dani007200964/Viking-Skull-Lamp/CAD/textures/galaxy_black_diffuse.png

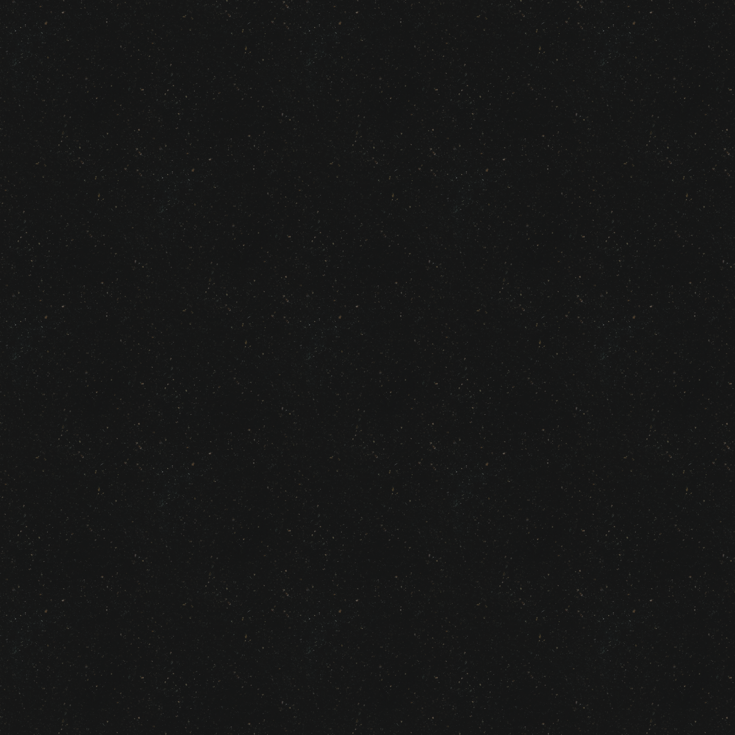
CAD/textures/galaxy_black_diffuse.png
