dani007200964/Viking-Skull-Lamp/CAD/textures/galaxy_black_specular.png

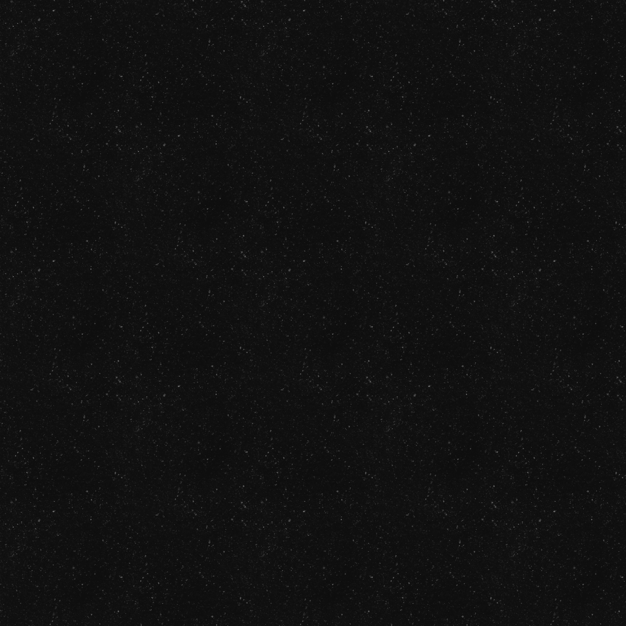
CAD/textures/galaxy_black_specular.png
