dani007200964/Viking-Skull-Lamp/docs/images/poster.png

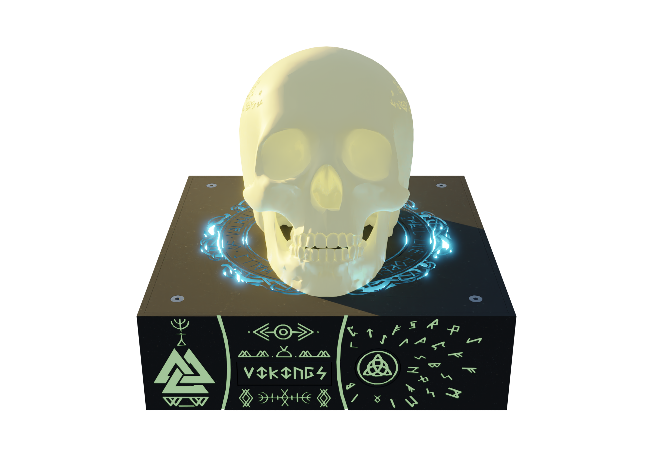
docs/html/poster.png
