dani007200964/Viking-Skull-Lamp/CAD/3mf/encoder_knob_with_art_1pcs.3mf

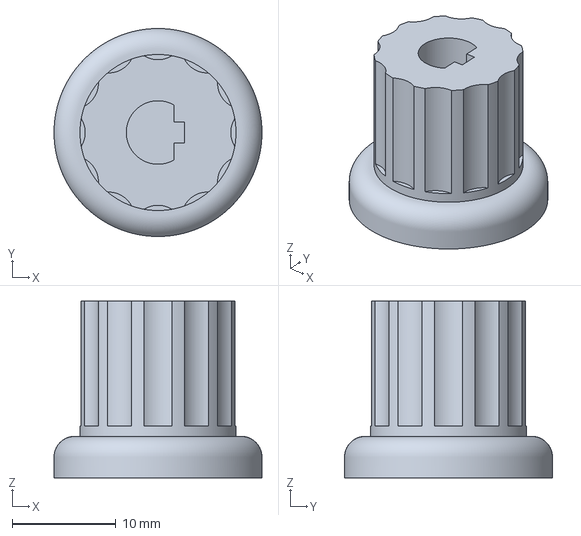
[picture p32: CAD file, 2022-09-24]
CAD/3mf/encoder_knob_with_art_1pcs.3mf
20.0 x 20.0 x 17.0 mm
