dani007200964/Viking-Skull-Lamp/CAD/3mf/led_ring_mount_1pcs.3mf

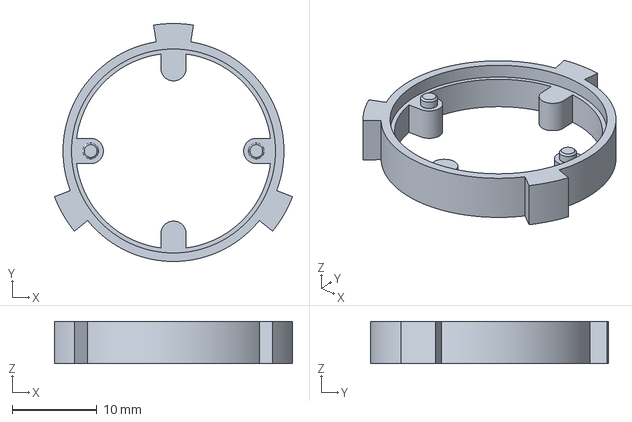
[picture p33: CAD file, 2022-09-24]
CAD/3mf/led_ring_mount_1pcs.3mf
28.0 x 28.0 x 5.00 mm
