dani007200964/Viking-Skull-Lamp/docs/html/box_front_with_art_1pcs.3mf

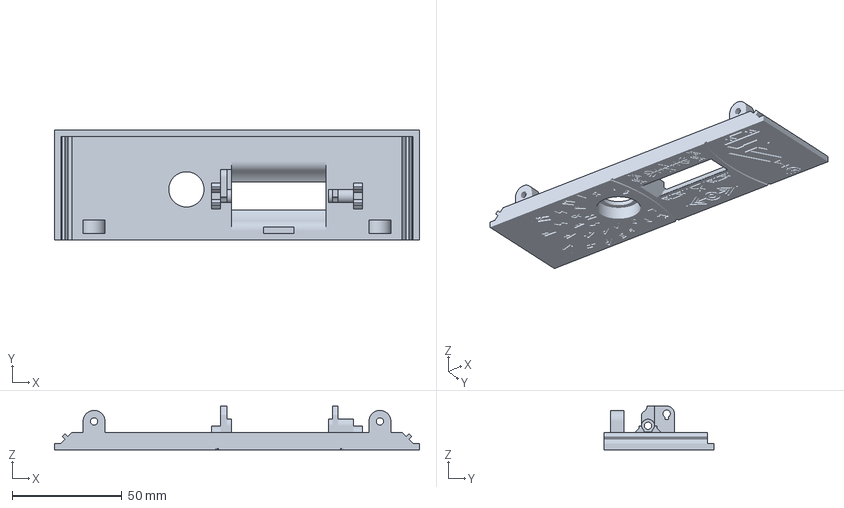
[picture p34: CAD file, 2022-09-24]
docs/html/box_front_with_art_1pcs.3mf
166.0 x 50.0 x 20.0 mm
