dani007200964/Viking-Skull-Lamp/CAD/3mf/display_holder_base_with_art_1pcs.3mf

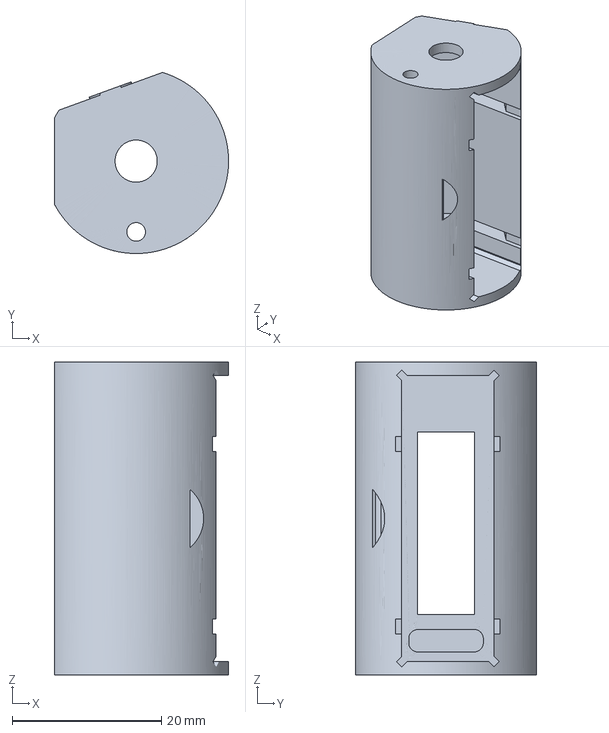
[picture p35: CAD file, 2022-09-24]
CAD/3mf/display_holder_base_with_art_1pcs.3mf
23.4 x 24.3 x 42.0 mm
