dani007200964/Viking-Skull-Lamp/docs/html/box_front_naked_1pcs.stl

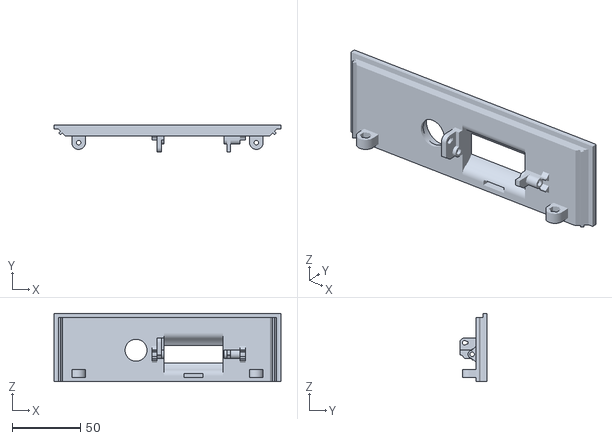
[picture p36: CAD file, 2022-09-02]
docs/html/box_front_naked_1pcs.stl
166.0 x 20.0 x 50.0
