dani007200964/Viking-Skull-Lamp/docs/html/display_holder_naked_1pcs.stl

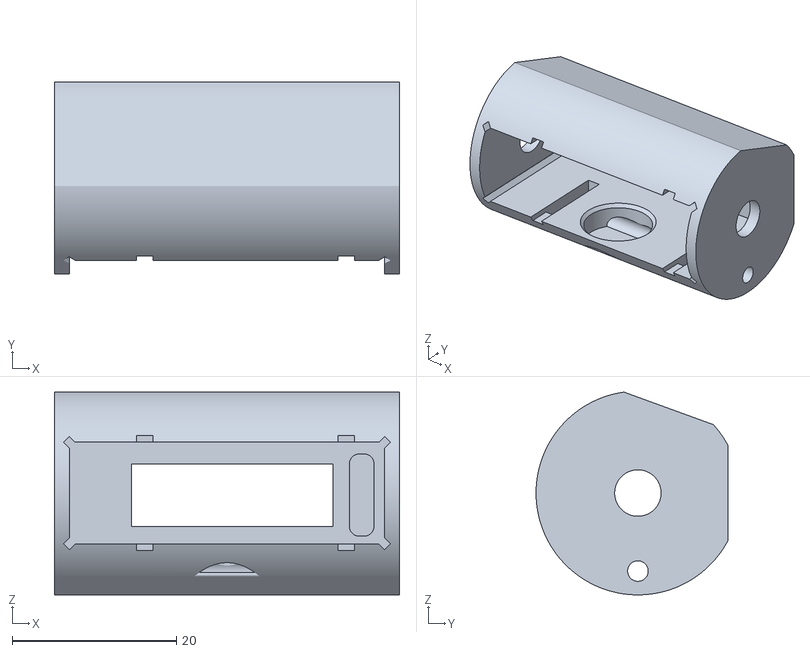
[picture p37: CAD file, 2022-09-02]
docs/html/display_holder_naked_1pcs.stl
42.0 x 23.4 x 24.7
