dani007200964/Viking-Skull-Lamp/docs/html/encoder_knob_naked_1pcs.stl

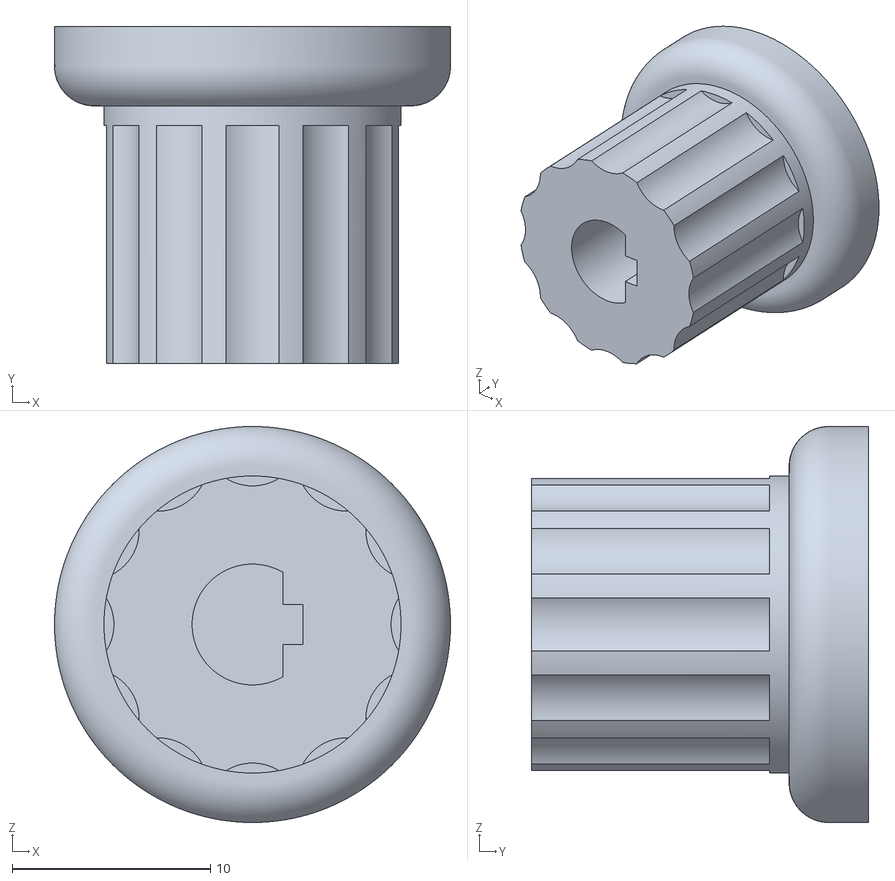
[picture p38: CAD file, 2022-09-02]
docs/html/encoder_knob_naked_1pcs.stl
20.0 x 17.0 x 20.0
